smrini/QMK-20keyPad/Assets/20KeyPad-V1/Pictures/frame.4.png

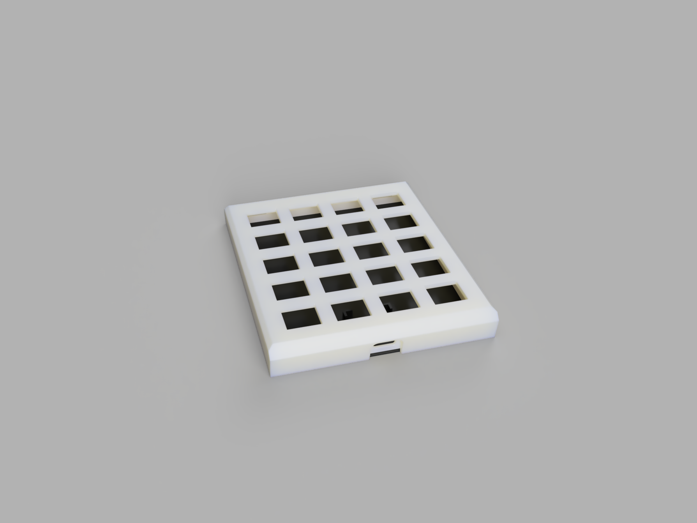
Assets/20KeyPad-V1/Pictures/frame.4.png
